JasonDinoPaws/Rumbi/Images/rumbi.webp

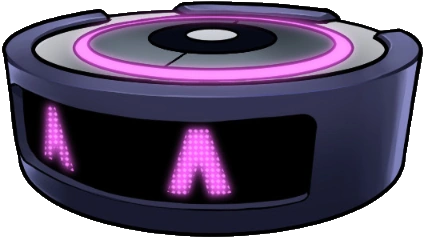
Images/rumbi.webp
