JasonDinoPaws/Rumbi/Stls/Motor/Wheel.stl

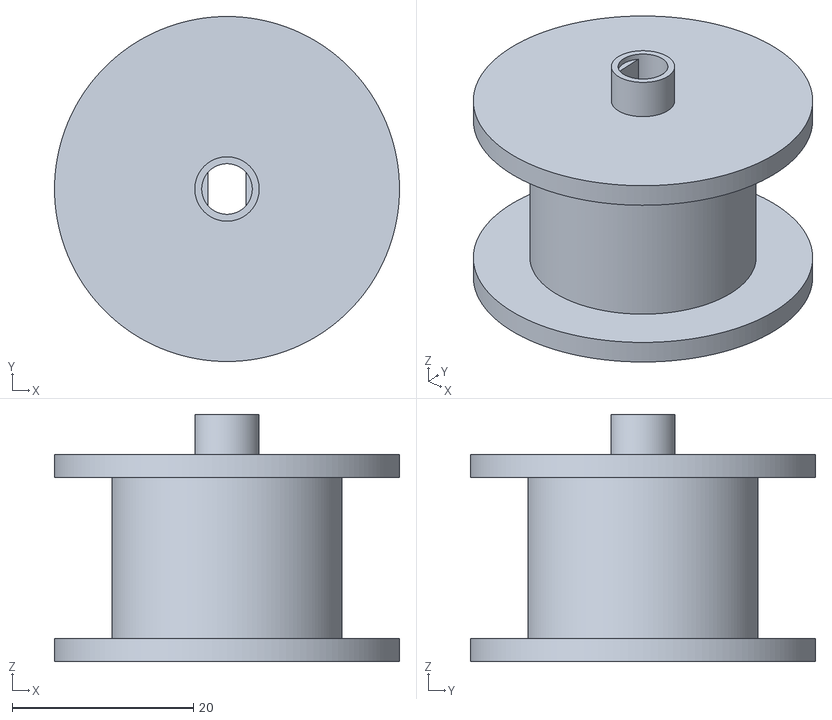
[picture p16: CAD file, 2026-01-09]
Stls/Motor/Wheel.stl
38.1 x 38.1 x 27.3
