JasonDinoPaws/Rumbi/Stls/Pi and battery/Battery holder.stl

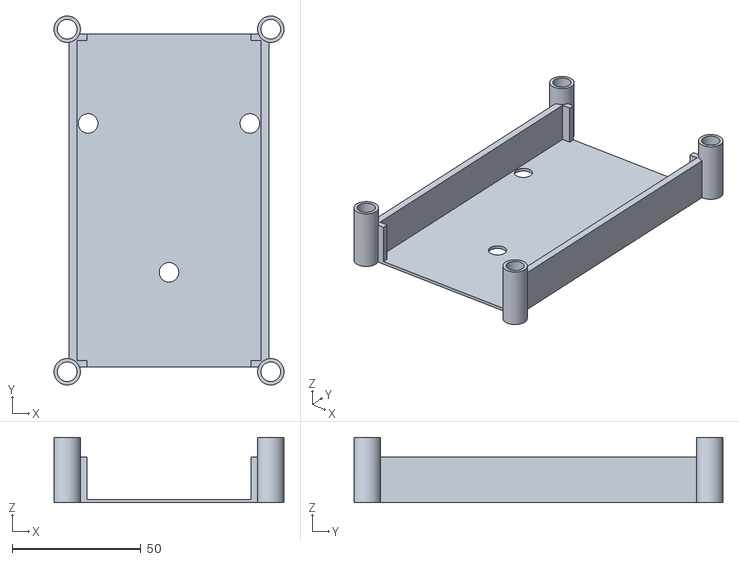
[picture p17: CAD file, 2026-01-09]
Stls/Pi and battery/Battery holder.stl
89.3 x 143.3 x 25.4
