JasonDinoPaws/Rumbi/Stls/Top/Roof conecters.stl

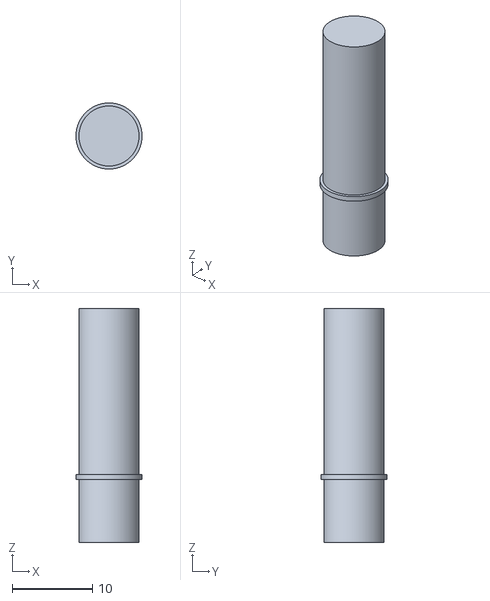
[picture p18: CAD file, 2026-01-09]
Stls/Top/Roof conecters.stl
8.26 x 8.26 x 29.2
