JasonDinoPaws/Rumbi/Stls/Walls/gray.stl

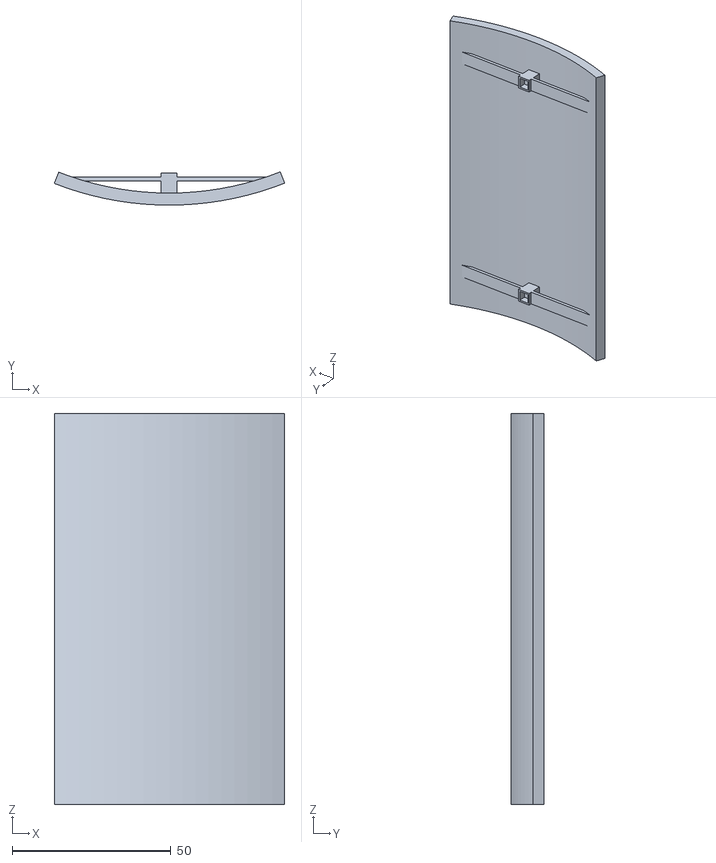
[picture p19: CAD file, 2026-01-09]
Stls/Walls/gray.stl
72.6 x 10.5 x 123.2
