JasonDinoPaws/Rumbi/Stls/Item Holder/Amplafiyer.stl

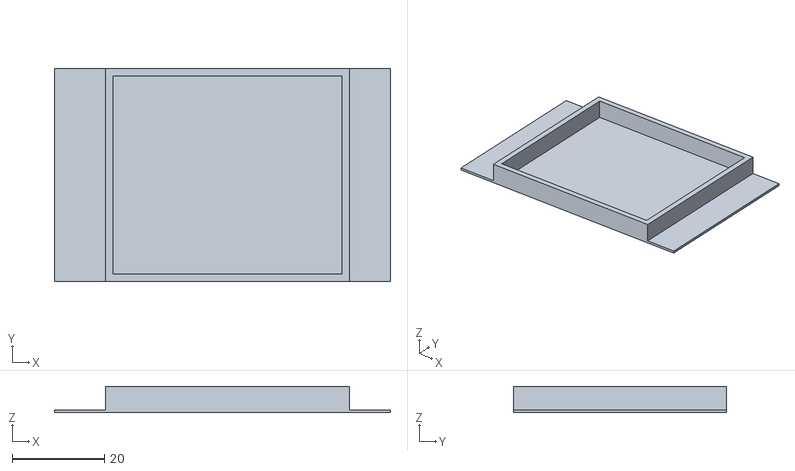
[picture p20: CAD file, 2026-01-09]
Stls/Item Holder/Amplafiyer.stl
72.7 x 46.0 x 5.72
