JasonDinoPaws/Rumbi/Stls/Motor/Lifter and cover.stl

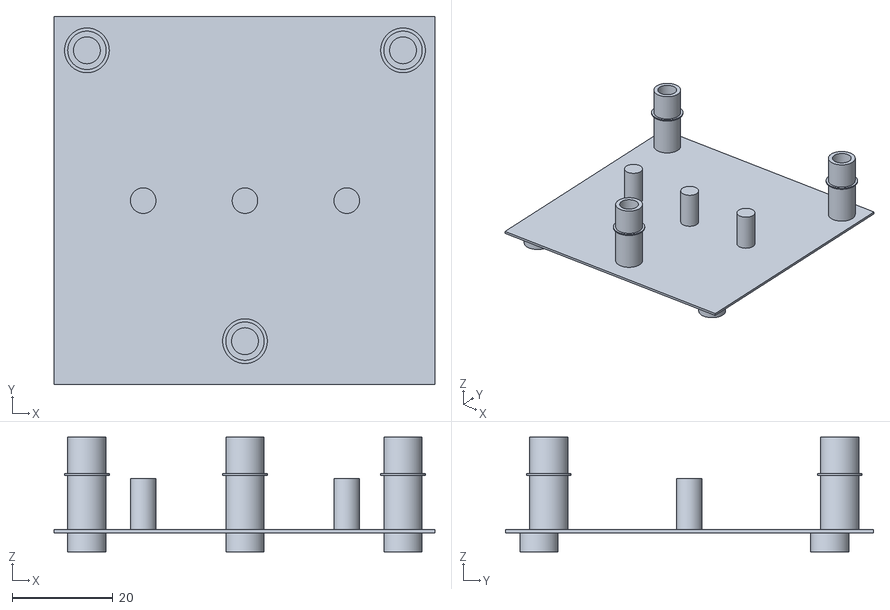
[picture p21: CAD file, 2026-01-09]
Stls/Motor/Lifter and cover.stl
75.7 x 73.2 x 22.9
