JasonDinoPaws/Rumbi/Stls/Top/Top exterdor-1.stl

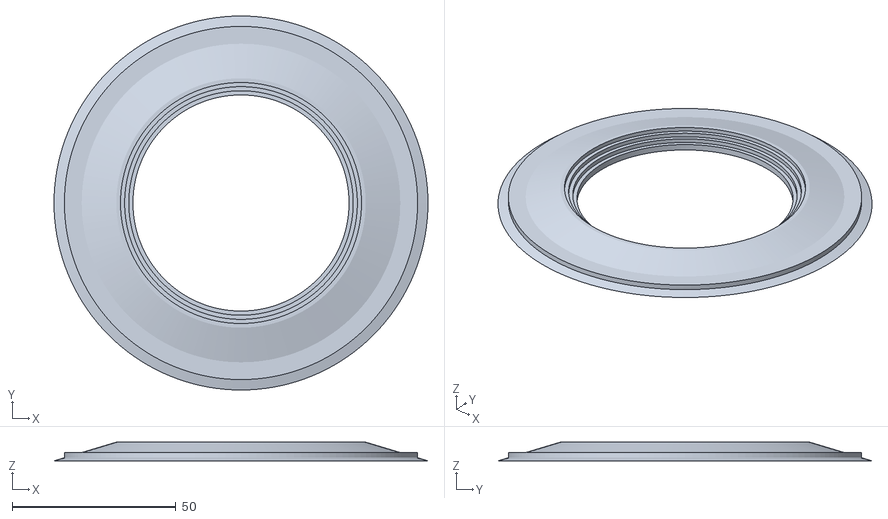
[picture p22: CAD file, 2026-01-09]
Stls/Top/Top exterdor-1.stl
114.3 x 114.3 x 5.72
