JasonDinoPaws/Rumbi/Stls/Walls/endofblack.stl

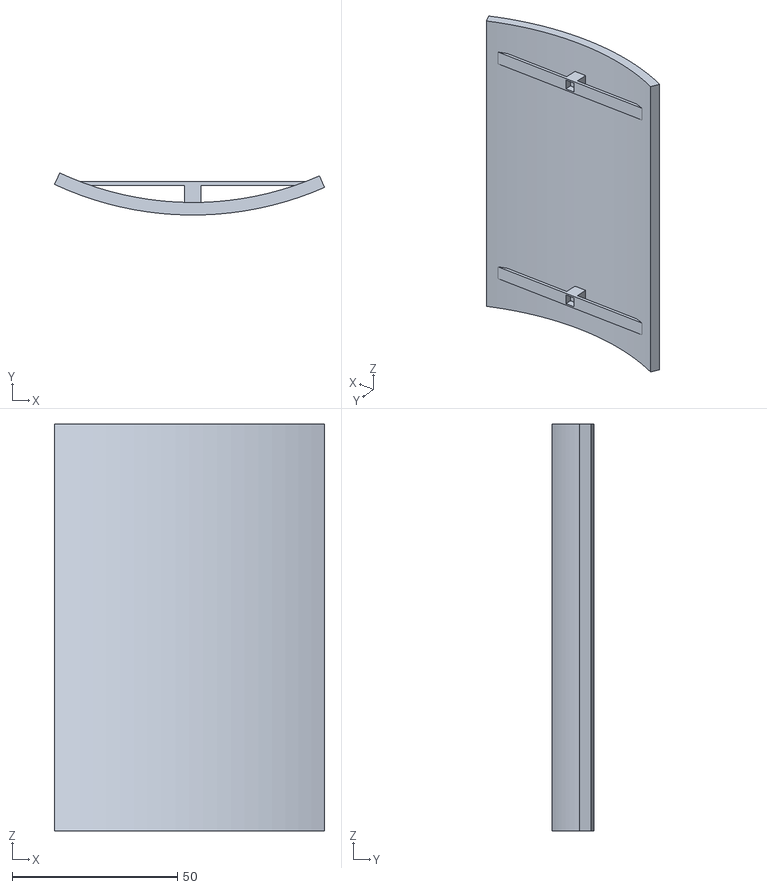
[picture p23: CAD file, 2026-01-09]
Stls/Walls/endofblack.stl
81.8 x 12.7 x 123.2
