JasonDinoPaws/Rumbi/Stls/Top/Cap.stl

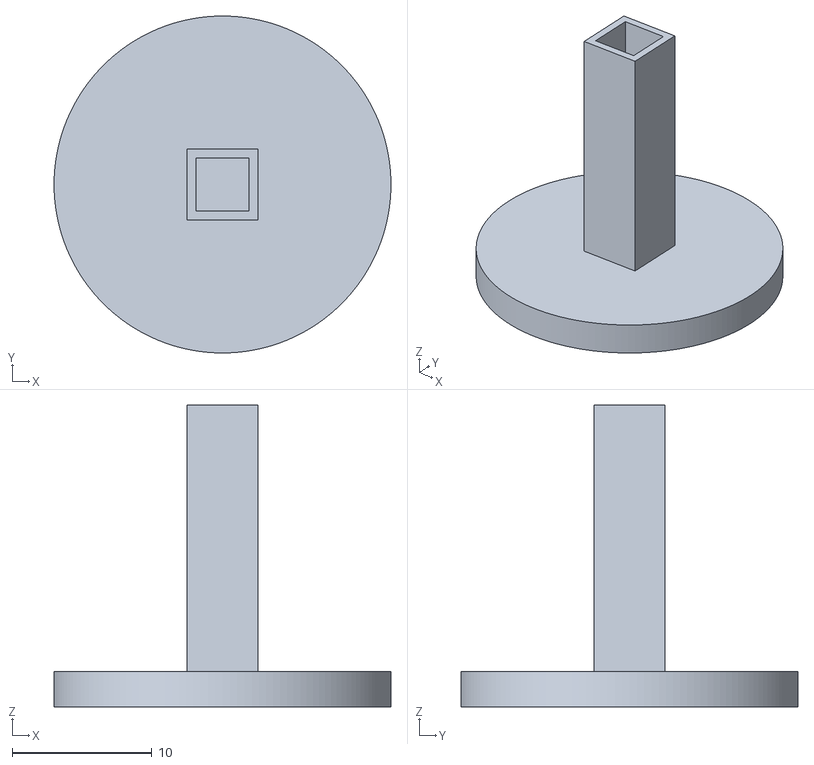
[picture p24: CAD file, 2026-01-09]
Stls/Top/Cap.stl
24.1 x 24.1 x 21.6
