JasonDinoPaws/Rumbi/Stls/Walls/Fan.stl

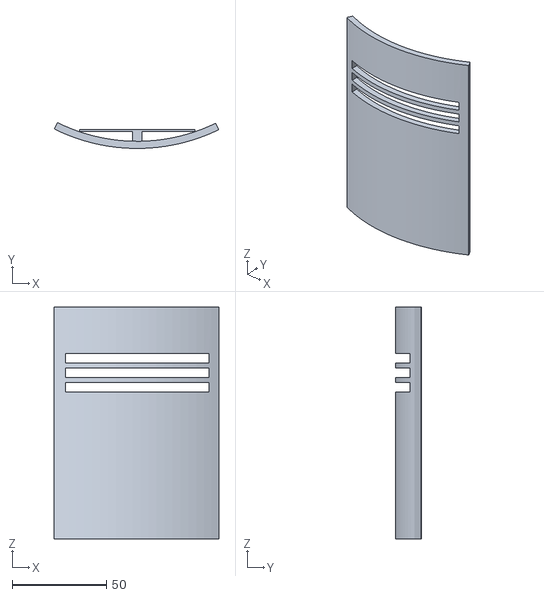
[picture p25: CAD file, 2026-01-09]
Stls/Walls/Fan.stl
87.4 x 13.7 x 123.2
